BigblenHD/Weather-balloon/Prep_launch/Module_software_tests/GPS/Working_GPS_Code/Working_GPS_Code.ino

/*
 * Rui Santos 
 * Complete Project Details https://randomnerdtutorials.com
 */
 
#include <SoftwareSerial.h>

// The serial connection to the GPS module
SoftwareSerial ss(1, 0);

void setup(){
  Serial.begin(9600);
  ss.begin(9600);
}

void loop(){
  while (ss.available() > 0){
    // get the byte data from the GPS
    byte gpsData = ss.read();
    Serial.write(gpsData);
  }
}
